thePunderWoman/SnipsControllers/include/menu.h

#pragma once

#include "calibration.h"
#include "complications.h"
#include "droid_store.h"
#include "power_management.h"
#include "screen.h"
#include "text_entry.h"
#include "droid_switcher.h"

// Pure on-device menu state machine. Knows nothing about real buttons or
// the display — SnipsController.ino translates physical button edges into
// the nav calls below (and detects the open combo via updateOpenCombo()),
// and renderMenuScreen() turns the current state into a ScreenBuffer for
// the (already-existing, hardware-touching) OledDisplay to draw.
enum class MenuScreen {
  kInactive,
  kMainMenu,
  kSwitchDroidList,
  kSwitchDroidResult,
  kManageDroidsList,
  kManageDroidsEnterName,
  kManageDroidsEnterPanId,
  kManageDroidsDeleteConfirm,
  kCalibrateStick,
  kStickDeadzone,
  kCalibrateTrigger,
  kDisplayConfig,
  kPowerConfig,
  kDeviceInfo,
  kButtonTest,
  kFactoryResetConfirm,
};

enum class MainMenuItem {
  kSwitchDroid = 0,
  kManageDroids,
  kCalibrateStick,
  kStickDeadzone,
  kCalibrateTrigger,
  kDisplayConfig,
  kPowerConfig,
  kDeviceInfo,
  kButtonTest,
  kFactoryReset,
  kCount,
};

// One row of the Power Config screen — Up/Down select a row, Enter
// cycles that row's value, same interaction pattern as Display Config's
// slots.
enum class PowerConfigRow {
  kMode = 0,
  kDimTimeout,
  kOffTimeout,
  kXbeeSleepTimeout,
  kAutoPoweroffTimeout,
  kCount,
};

const char *mainMenuItemLabel(MainMenuItem item);

class MenuController {
 public:
  MenuScreen currentScreen() const { return screen_; }
  MainMenuItem selectedMainMenuItem() const;

  // Held-combo detection to open the menu from kInactive — call every
  // loop tick with the current debounced state of the two buttons this
  // controller uses to enter the menu, regardless of currentScreen().
  void updateOpenCombo(bool comboButtonAPressed, bool comboButtonBPressed,
                       unsigned long nowMs);

  // Discrete nav events — call at most once per tick, only on a fresh
  // button-press edge (not while held). Meaning depends on the current
  // screen: list navigation on list screens, character scroll on text
  // entry screens.
  void onUp();
  void onDown();
  void onBack();

  // Enter needs the current raw analog readings so the calibration
  // screens can capture a sample at the moment of confirmation; ignored
  // by every other screen.
  void onEnter(int rawTrigger, int rawStickX, int rawStickY);

  // Call every loop tick regardless of button edges. Two independent
  // things happen here:
  //  - Stick calibration's "roll to extremes" step continuously tracks
  //    min/max from the raw readings — no-op unless currentScreen() ==
  //    kCalibrateStick and its internal flow is in the rolling step.
  //  - The stick doubles as menu Up/Down navigation (same effect as the
  //    Left Up/Down buttons) via stickYPercent, the already-calibrated
  //    reading — a threshold push counts as one discrete nav event, and
  //    the stick must return near center before it can fire again, so
  //    holding it doesn't spam repeated scrolls. Skipped entirely on
  //    kCalibrateStick, where stick position is the data being
  //    captured, not a nav input.
  // Returns true if it fired a nav event this call — SnipsController.ino
  // needs this to know when to redraw (see its menuStateChanged comment).
  bool tick(int rawStickX, int rawStickY, int stickYPercent);

  TriggerCalibrationFlow::Step triggerCalibrationStep() const {
    return triggerFlow_.currentStep();
  }
  StickCalibrationFlow::Step stickCalibrationStep() const {
    return stickFlow_.currentStep();
  }
  bool stickCalibrationHasEnoughRange() const {
    return stickFlow_.hasEnoughRange();
  }

  // Each returns true exactly once, the tick a new result becomes ready
  // to persist, and writes it into the output params.
  bool consumeNewTriggerCalibration(int *outMin, int *outMax);
  bool consumeNewStickCalibration(int *outCenterX, int *outCenterY,
                                   int *outMinX, int *outMaxX, int *outMinY,
                                   int *outMaxY);
  bool consumeFactoryResetConfirmed();

  // Button Test screen (bring-up/support tool — see PCB/README.md's
  // Bringup Sequence, step 4): records the most recent raw button press
  // for display, by index into Buttons::Index. While this screen is
  // active, SnipsController.ino routes every button's press edge here
  // instead of through the usual nav calls (onUp()/onDown()/onEnter()),
  // including the ones normally "stolen" for nav everywhere else —
  // except Bumper, which still exits the screen via onBack() same as any
  // other screen; that exit is itself the test for Bumper. No-op unless
  // this screen is active. -1 means "nothing pressed yet since the
  // screen was opened".
  void onButtonTestPress(size_t buttonIndex);
  int lastTestedButtonIndex() const { return lastTestedButtonIndex_; }

  // Droid management — the store is owned here so rendering/navigation
  // can see it directly; SnipsController.ino restores it from
  // DroidPersistence once at boot and re-persists it whenever
  // consumeDroidStoreChanged() reports a change.
  void setDroidStore(const DroidStore &store) { droidStore_ = store; }
  const DroidStore &droidStore() const { return droidStore_; }
  bool consumeDroidStoreChanged();

  // Switch Droid needs a way to actually talk to the radio — set once at
  // boot. May be left null (switching then always reports kNoTransport).
  void setXbeeTransport(XbeeTransport *transport) {
    xbeeTransport_ = transport;
  }

  // The XBee's own SL (queried once at boot, since it's a fixed hardware
  // address) for the Device Info screen — plain string storage, no
  // hardware access here.
  void setDeviceSerialLow(const char *hex) { deviceSerialLow_ = hex; }
  const char *deviceSerialLow() const { return deviceSerialLow_; }

  int selectedDroidListIndex() const { return droidListIndex_; }
  DroidSwitchResult lastSwitchResult() const { return lastSwitchResult_; }
  const TextEntryWidget &nameEntry() const { return nameEntry_; }
  const TextEntryWidget &panIdEntry() const { return panIdEntry_; }

  // The currently-active droid's name, for the complications system's
  // "Droid Name" source — "(none)" until either a switch succeeds or
  // setCurrentDroidName() seeds it. SnipsController.ino calls the setter
  // once at boot, having derived the name by querying the XBee module's
  // current PAN ID (which it remembers on its own — see
  // XbeeControl::queryPanId()) and matching it against the droid list.
  const char *currentDroidName() const { return currentDroidName_; }
  void setCurrentDroidName(const char *name);

  // Display Config edits an externally-owned ComplicationRegistry rather
  // than duplicating its slot-assignment state here — set once at boot.
  // May be left null (the menu screen then just does nothing on Enter).
  void setComplications(ComplicationRegistry *registry) {
    complications_ = registry;
  }
  const ComplicationRegistry *complications() const { return complications_; }
  int selectedDisplayConfigSlot() const { return displayConfigSlotIndex_; }
  bool consumeComplicationsChanged();

  // Power Config edits an externally-owned PowerConfig rather than
  // duplicating its state here — set once at boot, same pattern as
  // setComplications(). May be left null (the menu screen then just
  // does nothing on Enter).
  void setPowerConfig(PowerConfig *config) { powerConfig_ = config; }
  const PowerConfig *powerConfig() const { return powerConfig_; }
  PowerConfigRow selectedPowerConfigRow() const {
    return static_cast<PowerConfigRow>(powerConfigRowIndex_);
  }
  bool consumePowerConfigChanged();

  // Stick deadzone: unlike Display/Power Config, this isn't an
  // externally-owned pointer — it's a plain value MenuController tracks
  // itself (SnipsController.ino seeds it once at boot from the loaded
  // CalibrationData, same pattern as setDeviceSerialLow()), since
  // there's only one value and no natural external owner the way
  // ComplicationRegistry/PowerConfig are owned elsewhere. Up/Down apply
  // a change immediately (see onUp()/onDown()) rather than needing a
  // separate Enter-to-confirm step.
  void setStickDeadzonePercent(int percent) {
    stickDeadzonePercent_ = percent;
  }
  int stickDeadzonePercent() const { return stickDeadzonePercent_; }
  bool consumeStickDeadzoneChanged();

 private:
  static constexpr unsigned long kOpenComboHoldMs = 1000;

  void open();
  void enterMainMenuItem(MainMenuItem item);
  static int wrapIndex(int index, int count);

  MenuScreen screen_ = MenuScreen::kInactive;
  int mainMenuIndex_ = 0;

  bool comboHeld_ = false;
  unsigned long comboStartMs_ = 0;

  TriggerCalibrationFlow triggerFlow_;
  StickCalibrationFlow stickFlow_;

  bool hasNewTriggerCalibration_ = false;
  int pendingTriggerMin_ = 0;
  int pendingTriggerMax_ = 0;

  bool hasNewStickCalibration_ = false;
  int pendingStickCenterX_ = 0;
  int pendingStickCenterY_ = 0;
  int pendingStickMinX_ = 0;
  int pendingStickMaxX_ = 0;
  int pendingStickMinY_ = 0;
  int pendingStickMaxY_ = 0;

  bool factoryResetConfirmed_ = false;

  int lastTestedButtonIndex_ = -1;

  // Re-armed once stickYPercent returns near center — see tick().
  bool stickNavArmed_ = true;

  DroidStore droidStore_;
  int droidListIndex_ = 0;
  bool droidStoreChanged_ = false;
  TextEntryWidget nameEntry_{TextEntryWidget::CharSet::kAlphanumeric};
  TextEntryWidget panIdEntry_{TextEntryWidget::CharSet::kHex};
  DroidSwitchResult lastSwitchResult_ = DroidSwitchResult::kSuccess;
  XbeeTransport *xbeeTransport_ = nullptr;
  const char *deviceSerialLow_ = "(unknown)";
  char currentDroidName_[DroidEntry::kMaxNameLength + 1] = "(none)";

  ComplicationRegistry *complications_ = nullptr;
  int displayConfigSlotIndex_ = 0;
  bool complicationsChanged_ = false;

  PowerConfig *powerConfig_ = nullptr;
  int powerConfigRowIndex_ = 0;
  bool powerConfigChanged_ = false;

  int stickDeadzonePercent_ = StickDeadzoneOptions::kPercents[1];
  bool stickDeadzoneChanged_ = false;
};

// Decides what text should be on screen for the menu's current state.
// Pure — takes no display dependency, just fills in a ScreenBuffer.
void renderMenuScreen(const MenuController &menu, ScreenBuffer *screen);
