thePunderWoman/SnipsControllers/src/menu.cpp

#include "menu.h"

#include <cstdio>
#include <cstring>

#include "buttons.h"
#include "firmware_version.h"

namespace {
// A 64-bit all-zero PAN ID — Digi's convention for "unconfigured," used
// by Factory Reset to make sure the radio doesn't quietly stay
// associated with whatever droid it was last on. See the
// kFactoryResetConfirm case in MenuController::onEnter().
constexpr const char *kClearedPanId = "0000000000000000";

// Stick-as-nav thresholds (see MenuController::tick()) — percentages of
// calibrated travel, not raw ADC. Sign convention (positive = up,
// negative = down) confirmed against real hardware. The fire threshold
// was originally 60 but real bring-up testing found that too demanding
// — even a full physical push doesn't reliably reach that percentage in
// every direction on real hardware (calibration accuracy varies by
// direction), so it effectively made "up" not work at all. Lowered to
// 25, with the rearm threshold dropped to match and keep a similar
// proportional hysteresis gap (prevents rapid double-firing right at
// the boundary).
constexpr int kStickNavFireThreshold = 25;
constexpr int kStickNavRearmThreshold = 10;
}  // namespace

const char *mainMenuItemLabel(MainMenuItem item) {
  switch (item) {
    case MainMenuItem::kSwitchDroid: return "Switch Droid";
    case MainMenuItem::kManageDroids: return "Manage Droids";
    case MainMenuItem::kCalibrateStick: return "Calibrate Stick";
    case MainMenuItem::kStickDeadzone: return "Stick Deadzone";
    case MainMenuItem::kCalibrateTrigger: return "Calibrate Trigger";
    case MainMenuItem::kDisplayConfig: return "Display Config";
    case MainMenuItem::kPowerConfig: return "Power Management";
    case MainMenuItem::kDeviceInfo: return "Device Info";
    case MainMenuItem::kButtonTest: return "Button Test";
    case MainMenuItem::kFactoryReset: return "Factory Reset";
    default: return "Unknown";
  }
}

MainMenuItem MenuController::selectedMainMenuItem() const {
  return static_cast<MainMenuItem>(mainMenuIndex_);
}

void MenuController::setCurrentDroidName(const char *name) {
  std::strncpy(currentDroidName_, name, sizeof(currentDroidName_) - 1);
  currentDroidName_[sizeof(currentDroidName_) - 1] = '\0';
}

int MenuController::wrapIndex(int index, int count) {
  if (count <= 0) return 0;
  return (index % count + count) % count;
}

void MenuController::open() {
  if (screen_ != MenuScreen::kInactive) return;
  screen_ = MenuScreen::kMainMenu;
  mainMenuIndex_ = 0;
}

void MenuController::updateOpenCombo(bool comboButtonAPressed,
                                     bool comboButtonBPressed,
                                     unsigned long nowMs) {
  if (comboButtonAPressed && comboButtonBPressed) {
    if (!comboHeld_) {
      comboHeld_ = true;
      comboStartMs_ = nowMs;
    } else if (nowMs - comboStartMs_ >= kOpenComboHoldMs) {
      open();
      comboHeld_ = false;  // avoid immediately retriggering
    }
  } else {
    comboHeld_ = false;
  }
}

void MenuController::onUp() {
  switch (screen_) {
    case MenuScreen::kMainMenu:
      mainMenuIndex_ = wrapIndex(mainMenuIndex_ - 1,
                                static_cast<int>(MainMenuItem::kCount));
      break;
    case MenuScreen::kSwitchDroidList:
      if (droidStore_.count() > 0) {
        droidListIndex_ = wrapIndex(droidListIndex_ - 1,
                                    static_cast<int>(droidStore_.count()));
      }
      break;
    case MenuScreen::kManageDroidsList:
      droidListIndex_ = wrapIndex(
          droidListIndex_ - 1, static_cast<int>(droidStore_.count()) + 1);
      break;
    case MenuScreen::kManageDroidsEnterName:
      nameEntry_.scrollPrev();
      break;
    case MenuScreen::kManageDroidsEnterPanId:
      panIdEntry_.scrollPrev();
      break;
    case MenuScreen::kDisplayConfig:
      displayConfigSlotIndex_ =
          wrapIndex(displayConfigSlotIndex_ - 1, ComplicationRegistry::kSlotCount);
      break;
    case MenuScreen::kPowerConfig:
      powerConfigRowIndex_ = wrapIndex(
          powerConfigRowIndex_ - 1, static_cast<int>(PowerConfigRow::kCount));
      break;
    case MenuScreen::kStickDeadzone:
      stickDeadzonePercent_ = nextDeadzonePercent(stickDeadzonePercent_);
      stickDeadzoneChanged_ = true;
      break;
    default:
      break;
  }
}

void MenuController::onDown() {
  switch (screen_) {
    case MenuScreen::kMainMenu:
      mainMenuIndex_ = wrapIndex(mainMenuIndex_ + 1,
                                static_cast<int>(MainMenuItem::kCount));
      break;
    case MenuScreen::kSwitchDroidList:
      if (droidStore_.count() > 0) {
        droidListIndex_ = wrapIndex(droidListIndex_ + 1,
                                    static_cast<int>(droidStore_.count()));
      }
      break;
    case MenuScreen::kManageDroidsList:
      droidListIndex_ = wrapIndex(
          droidListIndex_ + 1, static_cast<int>(droidStore_.count()) + 1);
      break;
    case MenuScreen::kManageDroidsEnterName:
      nameEntry_.scrollNext();
      break;
    case MenuScreen::kManageDroidsEnterPanId:
      panIdEntry_.scrollNext();
      break;
    case MenuScreen::kDisplayConfig:
      displayConfigSlotIndex_ =
          wrapIndex(displayConfigSlotIndex_ + 1, ComplicationRegistry::kSlotCount);
      break;
    case MenuScreen::kPowerConfig:
      powerConfigRowIndex_ = wrapIndex(
          powerConfigRowIndex_ + 1, static_cast<int>(PowerConfigRow::kCount));
      break;
    case MenuScreen::kStickDeadzone:
      stickDeadzonePercent_ = prevDeadzonePercent(stickDeadzonePercent_);
      stickDeadzoneChanged_ = true;
      break;
    default:
      break;
  }
}

void MenuController::onBack() {
  switch (screen_) {
    case MenuScreen::kMainMenu:
      screen_ = MenuScreen::kInactive;
      break;
    case MenuScreen::kSwitchDroidList:
    case MenuScreen::kSwitchDroidResult:
    case MenuScreen::kManageDroidsList:
      screen_ = MenuScreen::kMainMenu;
      break;
    case MenuScreen::kManageDroidsDeleteConfirm:
      screen_ = MenuScreen::kManageDroidsList;
      break;
    // Bumper always means "go back," same as every other screen — it
    // used to backspace one character at a time first and only actually
    // leave once the field was empty, which looked like it "didn't work"
    // to anyone who hadn't already cleared what they'd typed. Character
    // correction is still possible before committing (scroll with
    // Up/Down), just not after — a deliberate simplification in favor of
    // a predictable universal Back button.
    case MenuScreen::kManageDroidsEnterName:
    case MenuScreen::kManageDroidsEnterPanId:
      screen_ = MenuScreen::kManageDroidsList;
      break;
    case MenuScreen::kCalibrateStick:
      stickFlow_ = StickCalibrationFlow();
      screen_ = MenuScreen::kMainMenu;
      break;
    case MenuScreen::kCalibrateTrigger:
      triggerFlow_ = TriggerCalibrationFlow();
      screen_ = MenuScreen::kMainMenu;
      break;
    case MenuScreen::kStickDeadzone:
    case MenuScreen::kDisplayConfig:
    case MenuScreen::kPowerConfig:
    case MenuScreen::kDeviceInfo:
    case MenuScreen::kButtonTest:
    case MenuScreen::kFactoryResetConfirm:
      screen_ = MenuScreen::kMainMenu;
      break;
    case MenuScreen::kInactive:
      break;
  }
}

void MenuController::enterMainMenuItem(MainMenuItem item) {
  switch (item) {
    case MainMenuItem::kSwitchDroid:
      droidListIndex_ = 0;
      screen_ = MenuScreen::kSwitchDroidList;
      break;
    case MainMenuItem::kManageDroids:
      droidListIndex_ = 0;
      screen_ = MenuScreen::kManageDroidsList;
      break;
    case MainMenuItem::kCalibrateStick:
      stickFlow_ = StickCalibrationFlow();
      screen_ = MenuScreen::kCalibrateStick;
      break;
    case MainMenuItem::kStickDeadzone:
      screen_ = MenuScreen::kStickDeadzone;
      break;
    case MainMenuItem::kCalibrateTrigger:
      triggerFlow_ = TriggerCalibrationFlow();
      screen_ = MenuScreen::kCalibrateTrigger;
      break;
    case MainMenuItem::kDisplayConfig:
      displayConfigSlotIndex_ = 0;
      screen_ = MenuScreen::kDisplayConfig;
      break;
    case MainMenuItem::kPowerConfig:
      powerConfigRowIndex_ = 0;
      screen_ = MenuScreen::kPowerConfig;
      break;
    case MainMenuItem::kDeviceInfo:
      screen_ = MenuScreen::kDeviceInfo;
      break;
    case MainMenuItem::kButtonTest:
      lastTestedButtonIndex_ = -1;
      screen_ = MenuScreen::kButtonTest;
      break;
    case MainMenuItem::kFactoryReset:
      screen_ = MenuScreen::kFactoryResetConfirm;
      break;
    case MainMenuItem::kCount:
      break;
  }
}

void MenuController::onEnter(int rawTrigger, int rawStickX, int rawStickY) {
  switch (screen_) {
    case MenuScreen::kMainMenu:
      enterMainMenuItem(selectedMainMenuItem());
      break;

    case MenuScreen::kSwitchDroidList:
      if (droidStore_.count() > 0) {
        const DroidEntry &target = droidStore_.at(droidListIndex_);
        lastSwitchResult_ = DroidSwitcher::switchTo(target.panId, xbeeTransport_);
        if (lastSwitchResult_ == DroidSwitchResult::kSuccess) {
          setCurrentDroidName(target.name);
        }
        screen_ = MenuScreen::kSwitchDroidResult;
      }
      break;

    case MenuScreen::kSwitchDroidResult:
      screen_ = MenuScreen::kMainMenu;
      break;

    case MenuScreen::kManageDroidsList:
      if (droidListIndex_ == static_cast<int>(droidStore_.count())) {
        nameEntry_.reset(TextEntryWidget::CharSet::kAlphanumeric,
                         DroidEntry::kMaxNameLength);
        screen_ = MenuScreen::kManageDroidsEnterName;
      } else if (droidStore_.count() > 0) {
        screen_ = MenuScreen::kManageDroidsDeleteConfirm;
      }
      break;

    case MenuScreen::kManageDroidsEnterName:
      nameEntry_.commitChar();
      if (nameEntry_.done()) {
        panIdEntry_.reset(TextEntryWidget::CharSet::kHex,
                          DroidEntry::kMaxPanIdLength);
        screen_ = MenuScreen::kManageDroidsEnterPanId;
      }
      break;

    case MenuScreen::kManageDroidsEnterPanId:
      panIdEntry_.commitChar();
      if (panIdEntry_.done()) {
        if (panIdEntry_.length() == 0) {
          // An empty PAN ID would pad out to all zeros — the "unconfigured"
          // value Factory Reset uses — so start the entry over instead.
          panIdEntry_.reset(TextEntryWidget::CharSet::kHex,
                            DroidEntry::kMaxPanIdLength);
          break;
        }
        droidStore_.add(nameEntry_.text(), panIdEntry_.text());
        droidStoreChanged_ = true;
        droidListIndex_ = 0;
        screen_ = MenuScreen::kManageDroidsList;
      }
      break;

    case MenuScreen::kManageDroidsDeleteConfirm:
      droidStore_.remove(droidListIndex_);
      droidStoreChanged_ = true;
      droidListIndex_ = 0;
      screen_ = MenuScreen::kManageDroidsList;
      break;

    case MenuScreen::kCalibrateTrigger:
      triggerFlow_.confirmStep(rawTrigger);
      if (triggerFlow_.currentStep() ==
          TriggerCalibrationFlow::Step::kDone) {
        hasNewTriggerCalibration_ = true;
        pendingTriggerMin_ = triggerFlow_.min();
        pendingTriggerMax_ = triggerFlow_.max();
        screen_ = MenuScreen::kMainMenu;
      }
      break;

    case MenuScreen::kCalibrateStick:
      if (stickFlow_.currentStep() ==
          StickCalibrationFlow::Step::kAwaitingCenter) {
        stickFlow_.confirmCenter(rawStickX, rawStickY);
      } else if (stickFlow_.currentStep() ==
                 StickCalibrationFlow::Step::kRolling) {
        stickFlow_.confirmDone();
        if (stickFlow_.currentStep() == StickCalibrationFlow::Step::kDone) {
          hasNewStickCalibration_ = true;
          pendingStickCenterX_ = stickFlow_.centerX();
          pendingStickCenterY_ = stickFlow_.centerY();
          pendingStickMinX_ = stickFlow_.minX();
          pendingStickMaxX_ = stickFlow_.maxX();
          pendingStickMinY_ = stickFlow_.minY();
          pendingStickMaxY_ = stickFlow_.maxY();
          screen_ = MenuScreen::kMainMenu;
        }
      }
      break;

    case MenuScreen::kDisplayConfig:
      if (complications_ != nullptr) {
        complications_->cycleSlotSource(displayConfigSlotIndex_);
        complicationsChanged_ = true;
      }
      break;

    case MenuScreen::kPowerConfig:
      if (powerConfig_ != nullptr) {
        switch (selectedPowerConfigRow()) {
          case PowerConfigRow::kMode:
            powerConfig_->mode = nextPowerManagementMode(powerConfig_->mode);
            break;
          case PowerConfigRow::kDimTimeout:
            powerConfig_->dimTimeoutSec =
                nextCascadeTimeoutSec(powerConfig_->dimTimeoutSec);
            break;
          case PowerConfigRow::kOffTimeout:
            powerConfig_->offTimeoutSec =
                nextCascadeTimeoutSec(powerConfig_->offTimeoutSec);
            break;
          case PowerConfigRow::kXbeeSleepTimeout:
            powerConfig_->xbeeSleepTimeoutSec =
                nextCascadeTimeoutSec(powerConfig_->xbeeSleepTimeoutSec);
            break;
          case PowerConfigRow::kAutoPoweroffTimeout:
            powerConfig_->autoPoweroffTimeoutSec =
                nextPoweroffTimeoutSec(powerConfig_->autoPoweroffTimeoutSec);
            break;
          case PowerConfigRow::kCount:
            break;
        }
        powerConfigChanged_ = true;
      }
      break;

    case MenuScreen::kDeviceInfo:
      screen_ = MenuScreen::kMainMenu;
      break;

    // Not reached in normal operation — SnipsController.ino routes button
    // presses to onButtonTestPress() instead of onEnter() while this
    // screen is active (see its declaration in menu.h). Kept as an
    // explicit no-op case for switch exhaustiveness.
    case MenuScreen::kButtonTest:
      break;

    // No confirm step -- Up/Down apply and save the change immediately
    // (see onUp()/onDown()).
    case MenuScreen::kStickDeadzone:
      break;

    case MenuScreen::kFactoryResetConfirm:
      factoryResetConfirmed_ = true;
      droidStore_ = DroidStore();
      droidStoreChanged_ = true;
      // A factory reset should genuinely disconnect from whatever droid
      // this controller was last on — leaving it silently still joined
      // post-reset would be confusing. Clears the PAN ID to a neutral,
      // unconfigured value and forces an immediate leave — deliberately
      // no rejoinNetwork() call after, unlike a normal Switch Droid: it
      // should sit disconnected until the user explicitly picks a new
      // droid, not auto-associate with whatever it can find. Everything
      // else about the radio (SL, etc.) is untouched.
      if (xbeeTransport_ != nullptr) {
        xbeeTransport_->leaveNetwork();
        xbeeTransport_->setPanId(kClearedPanId);
      }
      setCurrentDroidName("(none)");
      screen_ = MenuScreen::kMainMenu;
      break;

    case MenuScreen::kInactive:
      break;
  }
}

void MenuController::onButtonTestPress(size_t buttonIndex) {
  if (screen_ != MenuScreen::kButtonTest) return;
  if (buttonIndex >= Buttons::kCount) return;
  lastTestedButtonIndex_ = static_cast<int>(buttonIndex);
}

bool MenuController::tick(int rawStickX, int rawStickY, int stickYPercent) {
  if (screen_ == MenuScreen::kCalibrateStick &&
      stickFlow_.currentStep() == StickCalibrationFlow::Step::kRolling) {
    stickFlow_.sample(rawStickX, rawStickY);
  }

  if (screen_ == MenuScreen::kCalibrateStick) return false;

  if (stickNavArmed_) {
    if (stickYPercent >= kStickNavFireThreshold) {
      onUp();
      stickNavArmed_ = false;
      return true;
    } else if (stickYPercent <= -kStickNavFireThreshold) {
      onDown();
      stickNavArmed_ = false;
      return true;
    }
  } else if (stickYPercent > -kStickNavRearmThreshold &&
             stickYPercent < kStickNavRearmThreshold) {
    stickNavArmed_ = true;
  }
  return false;
}

bool MenuController::consumeNewTriggerCalibration(int *outMin, int *outMax) {
  if (!hasNewTriggerCalibration_) return false;
  *outMin = pendingTriggerMin_;
  *outMax = pendingTriggerMax_;
  hasNewTriggerCalibration_ = false;
  return true;
}

bool MenuController::consumeNewStickCalibration(int *outCenterX,
                                                 int *outCenterY,
                                                 int *outMinX, int *outMaxX,
                                                 int *outMinY, int *outMaxY) {
  if (!hasNewStickCalibration_) return false;
  *outCenterX = pendingStickCenterX_;
  *outCenterY = pendingStickCenterY_;
  *outMinX = pendingStickMinX_;
  *outMaxX = pendingStickMaxX_;
  *outMinY = pendingStickMinY_;
  *outMaxY = pendingStickMaxY_;
  hasNewStickCalibration_ = false;
  return true;
}

bool MenuController::consumeFactoryResetConfirmed() {
  if (!factoryResetConfirmed_) return false;
  factoryResetConfirmed_ = false;
  return true;
}

bool MenuController::consumeDroidStoreChanged() {
  if (!droidStoreChanged_) return false;
  droidStoreChanged_ = false;
  return true;
}

bool MenuController::consumeComplicationsChanged() {
  if (!complicationsChanged_) return false;
  complicationsChanged_ = false;
  return true;
}

bool MenuController::consumePowerConfigChanged() {
  if (!powerConfigChanged_) return false;
  powerConfigChanged_ = false;
  return true;
}

bool MenuController::consumeStickDeadzoneChanged() {
  if (!stickDeadzoneChanged_) return false;
  stickDeadzoneChanged_ = false;
  return true;
}

namespace {

void renderTextEntryLine(const TextEntryWidget &widget, ScreenBuffer *screen,
                         int lineIndex) {
  char line[ScreenBuffer::kMaxLineLength + 1];
  if (widget.isDoneSelected()) {
    std::snprintf(line, sizeof(line), "%s[DONE]", widget.text());
  } else {
    std::snprintf(line, sizeof(line), "%s[%c]", widget.text(),
                  widget.currentChar());
  }
  screen->setLine(lineIndex, line);
}

const char *powerModeLabel(PowerManagementMode mode) {
  switch (mode) {
    case PowerManagementMode::kAlwaysOn: return "Always on";
    case PowerManagementMode::kDimOnly: return "Dim OLED";
    case PowerManagementMode::kDimAndOff: return "Dim+Off OLED";
    case PowerManagementMode::kDimOffAndXbeeSleep: return "+XBee sleep";
    default: return "Unknown";
  }
}

// Formats a duration in seconds as "Ns" below one minute, "Nm" at exact
// minutes (the only case that matters for the auto-poweroff row, whose
// options are all whole minutes).
void formatSeconds(int totalSeconds, char *out, size_t outCapacity) {
  if (totalSeconds % 60 == 0) {
    std::snprintf(out, outCapacity, "%dm", totalSeconds / 60);
  } else {
    std::snprintf(out, outCapacity, "%ds", totalSeconds);
  }
}

const char *switchResultText(DroidSwitchResult result) {
  switch (result) {
    case DroidSwitchResult::kSuccess: return "Success!";
    case DroidSwitchResult::kInvalidPanId: return "Invalid PAN ID";
    case DroidSwitchResult::kLeaveFailed: return "Leave failed";
    case DroidSwitchResult::kSetPanFailed: return "Set PAN failed";
    case DroidSwitchResult::kRejoinFailed: return "Rejoin failed";
    case DroidSwitchResult::kNoTransport: return "No XBee link";
    default: return "Unknown";
  }
}

}  // namespace

void renderMenuScreen(const MenuController &menu, ScreenBuffer *screen) {
  screen->clear();

  switch (menu.currentScreen()) {
    case MenuScreen::kInactive:
      break;  // caller decides what else to show when the menu is closed

    case MenuScreen::kMainMenu: {
      screen->setLine(0, "== Menu ==");
      char line[ScreenBuffer::kMaxLineLength + 1];
      // Scrolls to keep the selection visible once there are more items
      // than fit below the title line — see kVisibleRows below.
      constexpr int kVisibleRows = static_cast<int>(ScreenBuffer::kMaxLines) - 1;
      const int totalItems = static_cast<int>(MainMenuItem::kCount);
      const int selected = static_cast<int>(menu.selectedMainMenuItem());
      int windowStart = 0;
      if (totalItems > kVisibleRows) {
        windowStart = selected - (kVisibleRows - 1);
        if (windowStart < 0) windowStart = 0;
        const int maxStart = totalItems - kVisibleRows;
        if (windowStart > maxStart) windowStart = maxStart;
      }
      for (int row = 0; row < kVisibleRows && windowStart + row < totalItems;
          ++row) {
        const int i = windowStart + row;
        const auto item = static_cast<MainMenuItem>(i);
        std::snprintf(line, sizeof(line), "%s%s",
                      i == selected ? "> " : "  ", mainMenuItemLabel(item));
        screen->setLine(1 + row, line);
      }
      break;
    }

    case MenuScreen::kSwitchDroidList: {
      screen->setLine(0, "Switch Droid");
      if (menu.droidStore().count() == 0) {
        screen->setLine(1, "No droids saved");
        break;
      }
      char line[ScreenBuffer::kMaxLineLength + 1];
      // Only as many entries as fit fit on screen below the header — see
      // DroidStore::kMaxDroids vs. ScreenBuffer::kMaxLines.
      const size_t visible =
          menu.droidStore().count() < ScreenBuffer::kMaxLines - 1
              ? menu.droidStore().count()
              : ScreenBuffer::kMaxLines - 1;
      for (size_t i = 0; i < visible; ++i) {
        std::snprintf(line, sizeof(line), "%s%s",
                      static_cast<int>(i) == menu.selectedDroidListIndex()
                          ? "> "
                          : "  ",
                      menu.droidStore().at(i).name);
        screen->setLine(1 + i, line);
      }
      break;
    }

    case MenuScreen::kSwitchDroidResult:
      screen->setLine(0, "Switch Droid");
      screen->setLine(1, switchResultText(menu.lastSwitchResult()));
      screen->setLine(2, "Press Enter");
      break;

    case MenuScreen::kManageDroidsList: {
      screen->setLine(0, "Manage Droids");
      char line[ScreenBuffer::kMaxLineLength + 1];
      const size_t count = menu.droidStore().count();
      const size_t visible =
          count + 1 < ScreenBuffer::kMaxLines - 1
              ? count + 1
              : ScreenBuffer::kMaxLines - 1;
      for (size_t i = 0; i < visible; ++i) {
        const char *label =
            i < count ? menu.droidStore().at(i).name : "+ Add New";
        std::snprintf(line, sizeof(line), "%s%s",
                      static_cast<int>(i) == menu.selectedDroidListIndex()
                          ? "> "
                          : "  ",
                      label);
        screen->setLine(1 + i, line);
      }
      break;
    }

    case MenuScreen::kManageDroidsEnterName:
      screen->setLine(0, "Add Droid: Name");
      renderTextEntryLine(menu.nameEntry(), screen, 1);
      screen->setLine(2, "Up/Down: letter");
      screen->setLine(3, "Click: next");
      screen->setLine(4, "Back: delete/exit");
      break;

    case MenuScreen::kManageDroidsEnterPanId:
      screen->setLine(0, "Add Droid: PAN ID");
      renderTextEntryLine(menu.panIdEntry(), screen, 1);
      screen->setLine(2, "Up/Down: letter");
      screen->setLine(3, "Click: next");
      screen->setLine(4, "Back: delete/exit");
      break;

    case MenuScreen::kManageDroidsDeleteConfirm:
      screen->setLine(0, "Delete Droid?");
      screen->setLine(1, menu.droidStore().at(menu.selectedDroidListIndex()).name);
      screen->setLine(2, "Enter = confirm");
      screen->setLine(3, "Back = cancel");
      break;

    case MenuScreen::kCalibrateTrigger:
      screen->setLine(0, "Calibrate Trigger");
      switch (menu.triggerCalibrationStep()) {
        case TriggerCalibrationFlow::Step::kAwaitingRelease:
          screen->setLine(1, "Release trigger,");
          screen->setLine(2, "press Macro1");
          break;
        case TriggerCalibrationFlow::Step::kAwaitingFullPull:
          screen->setLine(1, "Pull fully,");
          screen->setLine(2, "press Macro1");
          break;
        case TriggerCalibrationFlow::Step::kDone:
          screen->setLine(1, "Done!");
          break;
      }
      break;

    case MenuScreen::kCalibrateStick:
      screen->setLine(0, "Calibrate Stick");
      switch (menu.stickCalibrationStep()) {
        case StickCalibrationFlow::Step::kAwaitingCenter:
          screen->setLine(1, "Center stick,");
          screen->setLine(2, "press Macro1");
          break;
        case StickCalibrationFlow::Step::kRolling:
          screen->setLine(1, "Rotate stick all the");
          screen->setLine(2, "way around 3 times,");
          screen->setLine(3, "return to center,");
          screen->setLine(4, menu.stickCalibrationHasEnoughRange()
                                 ? "then press Macro1"
                                 : "not enough yet");
          break;
        case StickCalibrationFlow::Step::kDone:
          screen->setLine(1, "Done!");
          break;
      }
      break;

    case MenuScreen::kStickDeadzone: {
      screen->setLine(0, "Stick Deadzone");
      char line[ScreenBuffer::kMaxLineLength + 1];
      std::snprintf(line, sizeof(line), "%d%%", menu.stickDeadzonePercent());
      screen->setLine(1, line);
      screen->setLine(2, "Up/Down: change");
      break;
    }

    case MenuScreen::kDisplayConfig: {
      screen->setLine(0, "Display Config");
      char line[ScreenBuffer::kMaxLineLength + 1];
      for (int i = 0; i < ComplicationRegistry::kSlotCount; ++i) {
        const char *sourceLabel =
            menu.complications() != nullptr
                ? complicationSourceLabel(menu.complications()->slotSource(i))
                : "(none)";
        std::snprintf(line, sizeof(line), "%s%d: %s",
                      i == menu.selectedDisplayConfigSlot() ? "> " : "  ",
                      i + 1, sourceLabel);
        screen->setLine(1 + i, line);
      }
      break;
    }

    case MenuScreen::kPowerConfig: {
      screen->setLine(0, "Power Management");
      const PowerConfig fallback;
      const PowerConfig &config =
          menu.powerConfig() != nullptr ? *menu.powerConfig() : fallback;
      char line[ScreenBuffer::kMaxLineLength + 1];
      char valueBuf[8];
      for (int i = 0; i < static_cast<int>(PowerConfigRow::kCount); ++i) {
        const char *rowPrefix = "";
        const char *rowValue = "";
        switch (static_cast<PowerConfigRow>(i)) {
          case PowerConfigRow::kMode:
            rowPrefix = "Mode: ";
            rowValue = powerModeLabel(config.mode);
            break;
          case PowerConfigRow::kDimTimeout:
            rowPrefix = "Dim: ";
            formatSeconds(config.dimTimeoutSec, valueBuf, sizeof(valueBuf));
            rowValue = valueBuf;
            break;
          case PowerConfigRow::kOffTimeout:
            rowPrefix = "Off: ";
            formatSeconds(config.offTimeoutSec, valueBuf, sizeof(valueBuf));
            rowValue = valueBuf;
            break;
          case PowerConfigRow::kXbeeSleepTimeout:
            rowPrefix = "XBee sleep: ";
            formatSeconds(config.xbeeSleepTimeoutSec, valueBuf,
                          sizeof(valueBuf));
            rowValue = valueBuf;
            break;
          case PowerConfigRow::kAutoPoweroffTimeout:
            rowPrefix = "Auto off: ";
            formatSeconds(config.autoPoweroffTimeoutSec, valueBuf,
                          sizeof(valueBuf));
            rowValue = valueBuf;
            break;
          case PowerConfigRow::kCount:
            break;
        }
        std::snprintf(line, sizeof(line), "%s%s%s",
                      i == static_cast<int>(menu.selectedPowerConfigRow())
                          ? "> "
                          : "  ",
                      rowPrefix, rowValue);
        screen->setLine(1 + i, line);
      }
      break;
    }

    case MenuScreen::kDeviceInfo: {
      screen->setLine(0, "Device Info");
      screen->setLine(1, "XBee SL:");
      screen->setLine(2, menu.deviceSerialLow());
      char line[ScreenBuffer::kMaxLineLength + 1];
      std::snprintf(line, sizeof(line), "FW: %s", Firmware::kVersion);
      screen->setLine(3, line);
      break;
    }

    case MenuScreen::kButtonTest:
      screen->setLine(0, "Button Test");
      if (menu.lastTestedButtonIndex() < 0) {
        screen->setLine(1, "Press any button");
      } else {
        char line[ScreenBuffer::kMaxLineLength + 1];
        std::snprintf(
            line, sizeof(line), "Pressed: %s",
            Buttons::name(static_cast<size_t>(menu.lastTestedButtonIndex())));
        screen->setLine(1, line);
      }
      screen->setLine(3, "Bumper = exit");
      break;

    case MenuScreen::kFactoryResetConfirm:
      screen->setLine(0, "Factory Reset?");
      screen->setLine(1, "Enter = confirm");
      screen->setLine(2, "Back = cancel");
      break;
  }
}
