thePunderWoman/SnipsControllers/include/snips_logo_bitmap.h

#pragma once

#include <cstdint>

// 1-bit Snips logo bitmap for the boot splash, generated from
// graphics/snips-logo.png (itself a 1:1 raster of graphics/snips-logo.svg)
// by thresholding its alpha channel at 48x64 — the largest size that fits
// the 128x64 OLED (Oled::kWidth/kHeight) while preserving the source
// canvas's aspect ratio. Regenerate by re-running that conversion if the
// source art changes; this file has no logic of its own, just packed
// pixel data in the row-major, MSB-first-per-byte format
// Adafruit_GFX::drawBitmap() expects.
namespace SnipsLogo {

constexpr int kWidth = 48;
constexpr int kHeight = 64;
constexpr int kByteWidth = (kWidth + 7) / 8;

constexpr uint8_t kBitmap[kByteWidth * kHeight] = {
    0x00, 0x00, 0x00, 0x00, 0x00, 0x00, 0x00, 0x00, 0x00, 0x00, 0x00, 0x00,
    0x00, 0x00, 0x00, 0x00, 0x00, 0x00, 0x00, 0x00, 0x00, 0x00, 0x00, 0x00,
    0x00, 0x00, 0x00, 0x00, 0x00, 0x00, 0x00, 0x00, 0x00, 0x40, 0x00, 0x00,
    0x00, 0x00, 0x00, 0x40, 0x00, 0x00, 0x00, 0x00, 0x00, 0x40, 0x00, 0x00,
    0x00, 0x00, 0x00, 0x40, 0x00, 0x00, 0x00, 0x00, 0x00, 0x40, 0x00, 0x00,
    0x00, 0x00, 0x00, 0x40, 0x04, 0x00, 0x00, 0x00, 0x00, 0x40, 0x08, 0x00,
    0x00, 0x00, 0x00, 0xc0, 0x08, 0x00, 0x00, 0x00, 0x00, 0xc0, 0x10, 0x00,
    0x00, 0x00, 0x00, 0xc0, 0x30, 0x00, 0x00, 0x00, 0x00, 0xc0, 0x20, 0x00,
    0x00, 0x00, 0x00, 0xc0, 0x60, 0x00, 0x00, 0x00, 0x00, 0xc0, 0xc0, 0x00,
    0x00, 0x00, 0x00, 0xc0, 0xc0, 0x00, 0x00, 0x00, 0x00, 0xc1, 0x80, 0x00,
    0x00, 0x00, 0x00, 0xc3, 0x00, 0x00, 0x00, 0x00, 0x00, 0xc3, 0x00, 0x00,
    0x00, 0x00, 0x01, 0xc6, 0x00, 0x00, 0x00, 0x00, 0x01, 0xce, 0x00, 0x00,
    0x00, 0x00, 0x01, 0xcc, 0x00, 0x00, 0x00, 0x00, 0x03, 0x5c, 0x00, 0x00,
    0x00, 0x00, 0x02, 0xf8, 0x00, 0x00, 0x00, 0x00, 0x05, 0xb8, 0x00, 0x00,
    0x00, 0x00, 0x0b, 0x1c, 0x00, 0x00, 0x00, 0x00, 0x12, 0x1c, 0x00, 0x00,
    0x00, 0x00, 0x24, 0x1c, 0x00, 0x00, 0x00, 0x00, 0x68, 0x1c, 0x00, 0x00,
    0x00, 0x00, 0x28, 0x1c, 0x00, 0x00, 0x00, 0x00, 0x34, 0x1c, 0x00, 0x00,
    0x00, 0x00, 0x1e, 0x7c, 0x00, 0x00, 0x00, 0x00, 0x0f, 0xfc, 0x00, 0x00,
    0x00, 0x00, 0x0f, 0xf0, 0x00, 0x00, 0x00, 0x00, 0x1f, 0xc0, 0x00, 0x00,
    0x00, 0x00, 0x39, 0xc0, 0x00, 0x00, 0x00, 0x00, 0x31, 0xc0, 0x00, 0x00,
    0x00, 0x00, 0x71, 0xc0, 0x00, 0x00, 0x00, 0x00, 0xe0, 0xc0, 0x00, 0x00,
    0x00, 0x00, 0xc0, 0xc0, 0x00, 0x00, 0x00, 0x03, 0x80, 0xc0, 0x00, 0x00,
    0x00, 0x1f, 0x00, 0xc0, 0x00, 0x00, 0x01, 0xff, 0x00, 0xc0, 0x00, 0x00,
    0x07, 0xff, 0x00, 0xc0, 0x00, 0x00, 0x07, 0xff, 0x01, 0xe0, 0x00, 0x00,
    0x07, 0xff, 0x01, 0x30, 0x00, 0x00, 0x07, 0xff, 0x02, 0x10, 0x00, 0x00,
    0x07, 0xff, 0x86, 0x08, 0x00, 0x00, 0x07, 0xff, 0x84, 0x04, 0x00, 0x00,
    0x03, 0xff, 0x88, 0x02, 0x00, 0x00, 0x03, 0xff, 0x90, 0x01, 0x00, 0x00,
    0x03, 0xff, 0x30, 0x01, 0x00, 0x00, 0x03, 0xf0, 0x10, 0x02, 0x00, 0x00,
    0x03, 0x00, 0x08, 0x06, 0x00, 0x00, 0x00, 0x00, 0x04, 0x04, 0x00, 0x00,
    0x00, 0x00, 0x02, 0x08, 0x00, 0x00, 0x00, 0x00, 0x03, 0x10, 0x00, 0x00,
    0x00, 0x00, 0x01, 0xb0, 0x00, 0x00, 0x00, 0x00, 0x00, 0xe0, 0x00, 0x00,
    0x00, 0x00, 0x00, 0x40, 0x00, 0x00, 0x00, 0x00, 0x00, 0x00, 0x00, 0x00,
};

}  // namespace SnipsLogo
